ChaudhryAsad/Project-Ontwerp/Altium/Componets.PNG

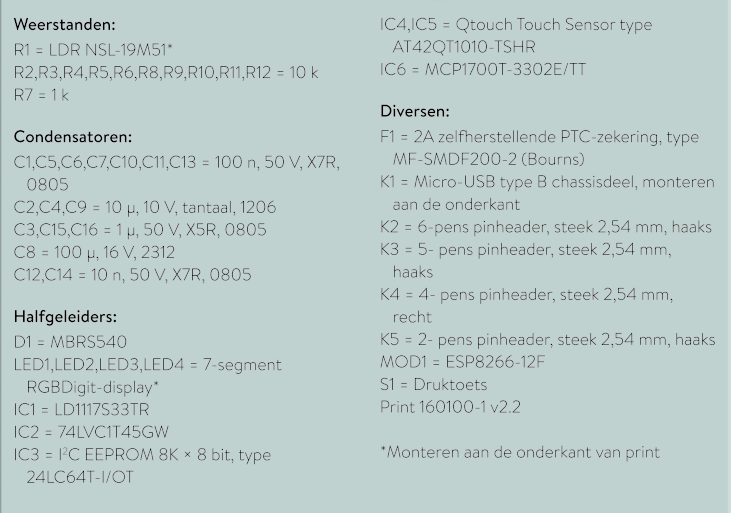
Altium/Componets.PNG
