ChaudhryAsad/Project-Ontwerp/Autocad/3box_3d.PNG

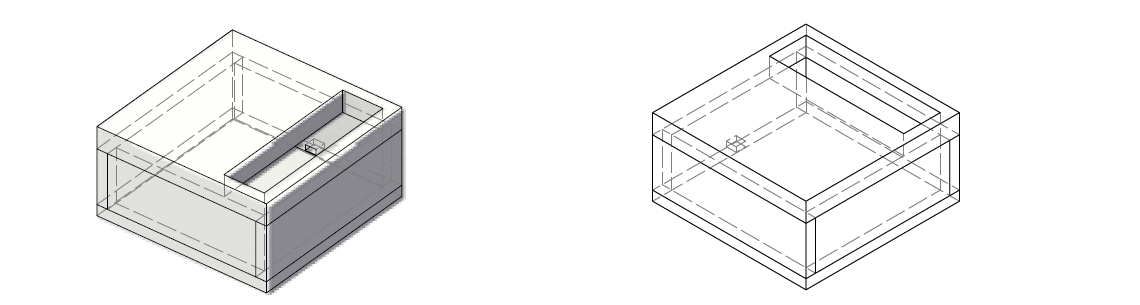
Autocad/3box_3d.PNG
