ChaudhryAsad/Project-Ontwerp/English/foto's/demo_colour.jpeg

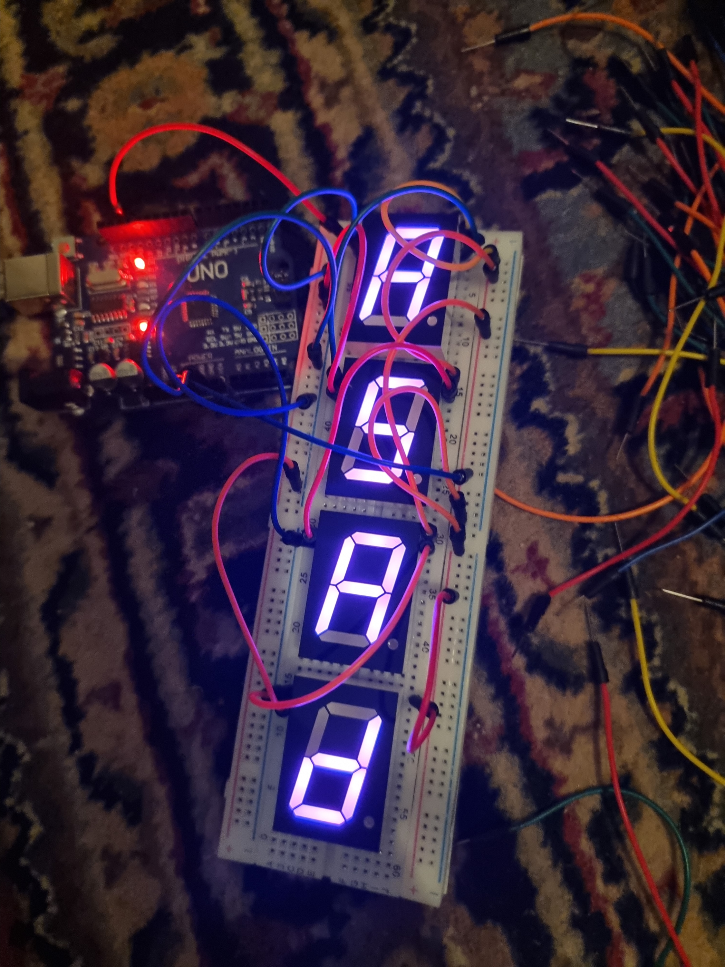
English/foto's/demo_colour.jpeg
