ChaudhryAsad/Project-Ontwerp/English/foto's/demo_no_colour.jpeg

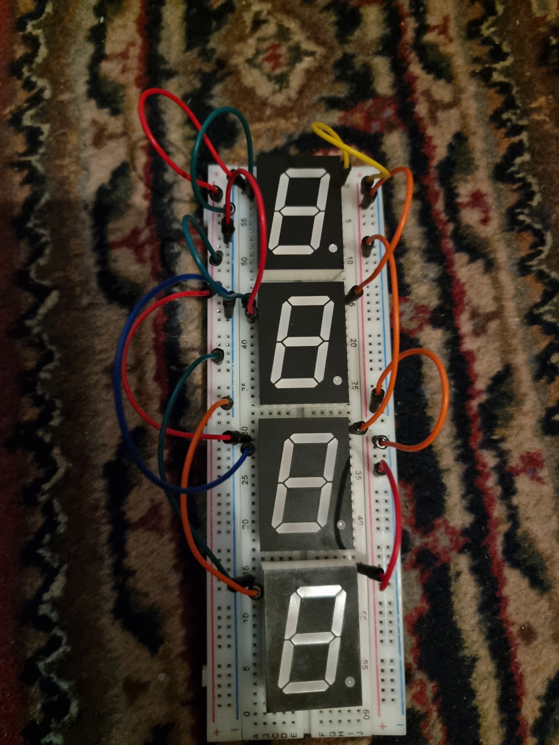
English/foto's/demo_no_colour.jpeg
