ChaudhryAsad/Project-Ontwerp/English/foto's/foot.PNG

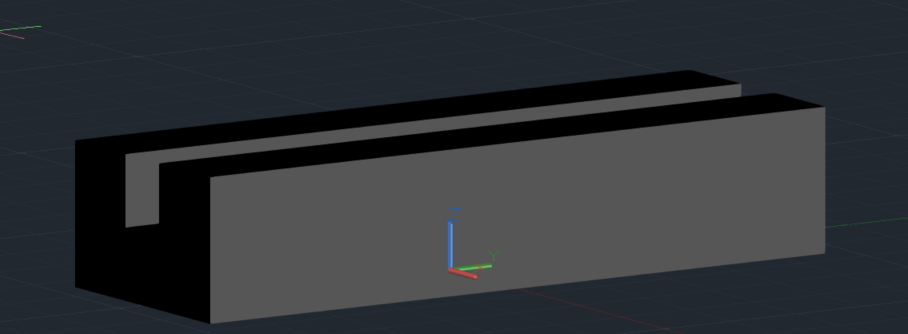
English/foto's/foot.PNG
