ChaudhryAsad/Project-Ontwerp/English/foto's/PCB_klaar.jpeg

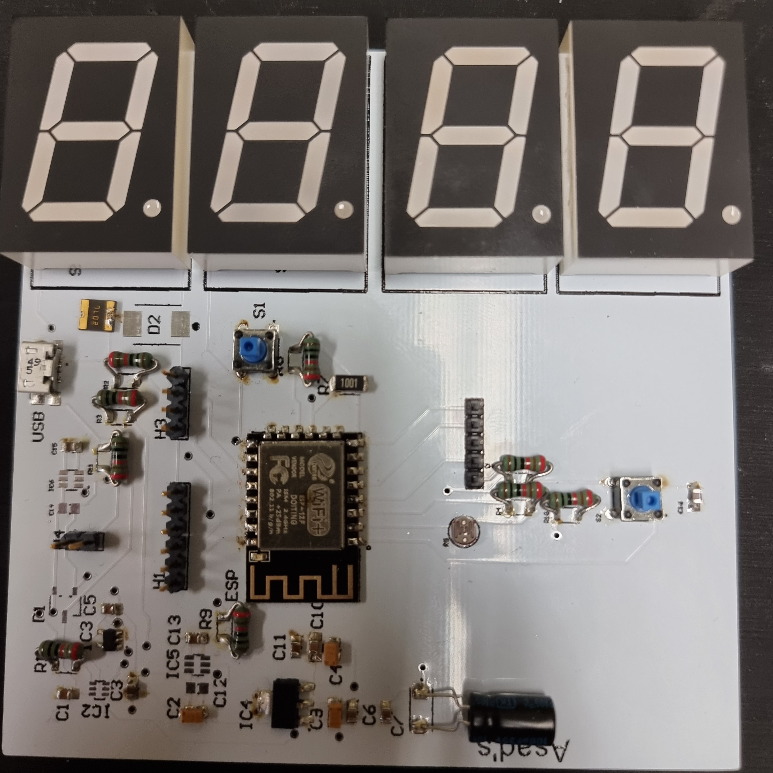
English/foto's/PCB_klaar.jpeg
