ChaudhryAsad/Project-Ontwerp/English/foto's/Pcb_verkeerd.jpeg

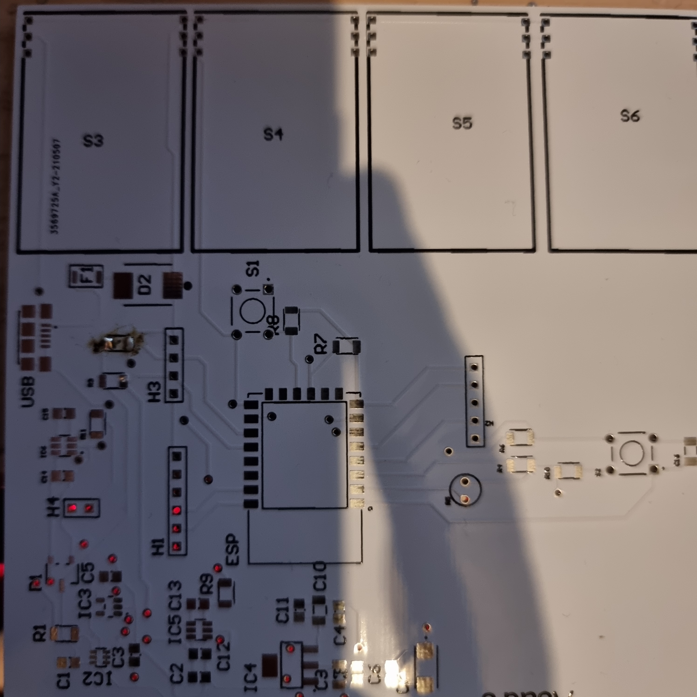
English/foto's/Pcb_verkeerd.jpeg
