ChaudhryAsad/Project-Ontwerp/English/foto's/Pcl_beetje.jpeg

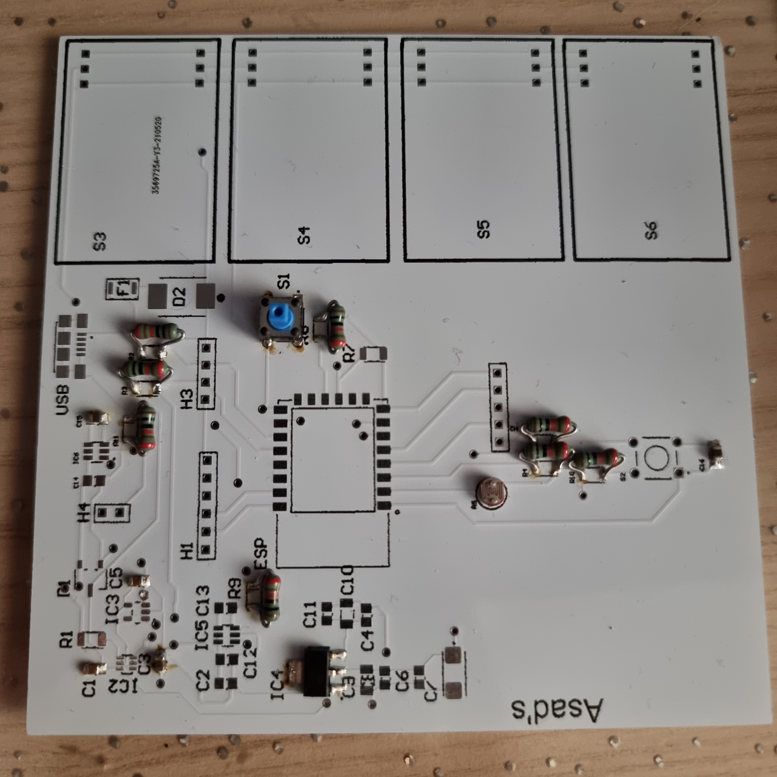
English/foto's/Pcl_beetje.jpeg
