ChaudhryAsad/Project-Ontwerp/English/foto's/Schema.PNG

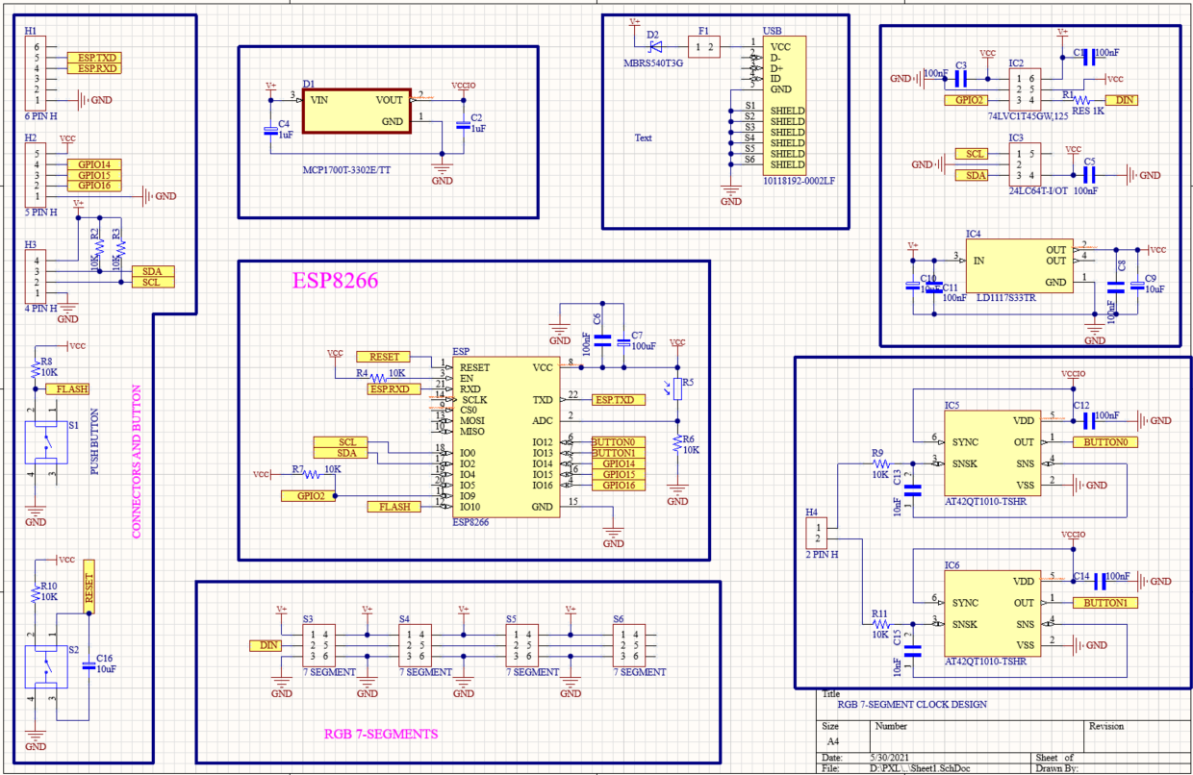
English/foto's/Schema.PNG
