ChaudhryAsad/Project-Ontwerp/English/foto's/order.PNG

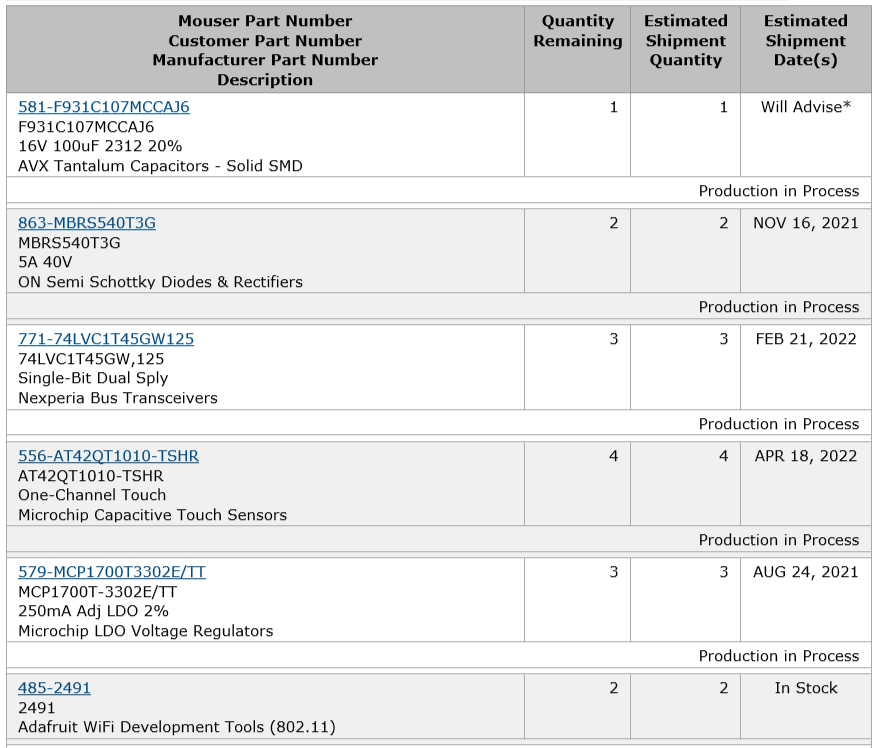
English/foto's/order.PNG
